shachi-lab/jjy_sim_esp32_C3_rev2/Source/JJY_Sim_ESP32_C3_REV2/shachi-lab_logo.h

// 'shachi-lab_LOGO_w128', 128x64px
const unsigned char shachilab_logo_bits[] = {
	0x00, 0x00, 0x03, 0x00, 0x00, 0x38, 0x60, 0x00, 0x07, 0x80, 0x01, 0x00, 0x00, 0x00, 0x00, 0x00, 
	0x00, 0x80, 0x03, 0x00, 0x00, 0x38, 0xe0, 0x00, 0x07, 0xc0, 0x01, 0x00, 0x00, 0x00, 0x00, 0x00, 
	0x00, 0x80, 0x03, 0x00, 0x00, 0x38, 0x60, 0x00, 0x07, 0xc0, 0x01, 0x00, 0x00, 0x00, 0x00, 0x00, 
	0x00, 0x80, 0x03, 0x00, 0x00, 0x38, 0x00, 0x00, 0x07, 0xc0, 0x03, 0x00, 0x00, 0x00, 0x00, 0x00, 
	0x00, 0x9e, 0x3f, 0xf8, 0xe1, 0xf9, 0x61, 0x3e, 0x87, 0xdf, 0x1f, 0xe0, 0xc3, 0xc3, 0xe6, 0x00, 
	0x00, 0xbf, 0x7f, 0xfc, 0xf9, 0xfb, 0xe3, 0x7f, 0xc7, 0xdf, 0x3f, 0xf0, 0xe7, 0xe7, 0xff, 0x01, 
	0x00, 0x97, 0x7f, 0xfe, 0xf9, 0xfb, 0xe7, 0x7e, 0xe7, 0xdf, 0x7f, 0xf0, 0xf7, 0xef, 0xff, 0x01, 
	0x00, 0x8f, 0xf7, 0xce, 0x3d, 0x39, 0xe7, 0x00, 0xe7, 0xdc, 0x7b, 0x78, 0x73, 0xee, 0xdf, 0x03, 
	0x00, 0xbf, 0xe3, 0xce, 0x1d, 0x38, 0xe7, 0x00, 0xe7, 0xdc, 0x73, 0x38, 0x78, 0xee, 0x9c, 0x03, 
	0x00, 0xbe, 0xe3, 0xce, 0x3d, 0x39, 0xe7, 0x00, 0xe7, 0xdc, 0x7b, 0x78, 0x73, 0xee, 0x9c, 0x03, 
	0x00, 0xbf, 0xe3, 0xfe, 0xf9, 0x3b, 0xe7, 0x00, 0xef, 0xdf, 0xff, 0xf3, 0xf7, 0xef, 0x9c, 0x03, 
	0x80, 0xbf, 0xe3, 0xfc, 0xf9, 0x3b, 0xe7, 0x00, 0xcf, 0xdf, 0xbf, 0xf7, 0xe7, 0xe7, 0x9c, 0x03, 
	0x00, 0x1f, 0xe3, 0xf8, 0xe1, 0x39, 0x66, 0x00, 0x8e, 0x9f, 0x1f, 0xe3, 0xc3, 0xe3, 0x9c, 0x01, 
	0x00, 0x00, 0x00, 0x00, 0x00, 0x00, 0x00, 0x00, 0x00, 0x00, 0x00, 0x00, 0x00, 0x00, 0x00, 0x00, 
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
	0x00, 0x00, 0x00, 0x01, 0x00, 0xf8, 0x7f, 0xf0, 0x0f, 0x00, 0x00, 0x0f, 0x70, 0x00, 0x00, 0x00, 
	0x00, 0x00, 0x00, 0x06, 0x00, 0xfb, 0x3f, 0xc0, 0x03, 0x00, 0x80, 0xf0, 0x1f, 0x00, 0x00, 0x00, 
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
};

const int shachilab_logo_width = 128;
const int shachilab_logo_height = 64;
